gaelperez16/raspberry-pi-2040-PCB-design/RP-2040 screenshots/3D viewer top side.jpg

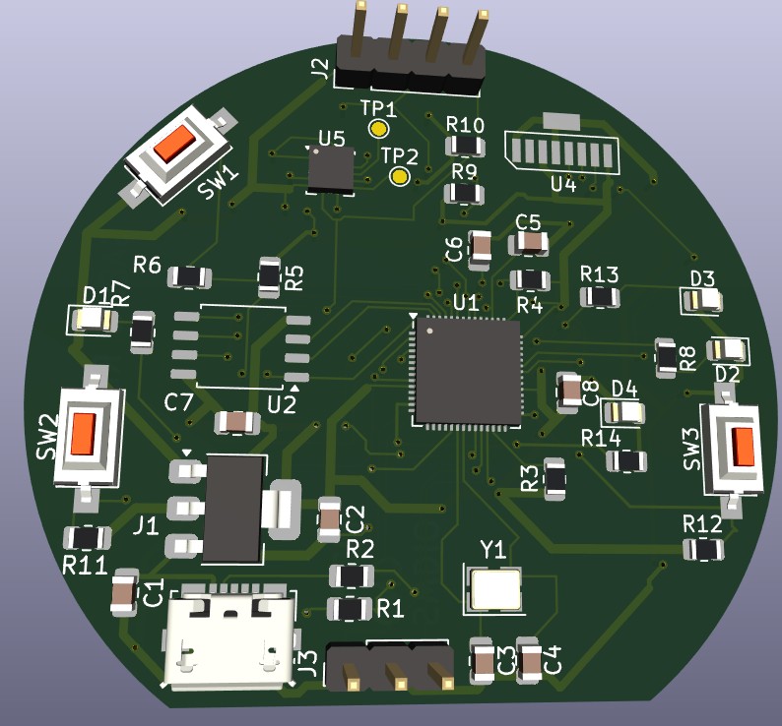
RP-2040 screenshots/3D viewer top side.jpg
